olup/grigri/software/src/player/player.h

#pragma once

#include <Arduino.h>

void player_init();

void player_stop();

void player_play(const char *path, int32_t position = -1);

void player_togglePause();

const bool player_isPlaying();

void player_moveRelative(int seconds);

uint32_t player_get_position();
void player_set_position(u_int32_t position);

void player_loop();

void audio_info(const char *info);
void audio_id3data(const char *info);
void audio_bitrate(const char *info);

void player_setVolume(uint8_t volume);
uint8_t player_get_volume();
